obehr/phoniebox_hat/simulation/CutOff.asc

B1: bv; P=2.5
C1: cap; 100n
C2: cap; 100n
C3: cap; 100n
D1: schottky
D2: schottky
M1: pmos; AO3401A
M2: nmos; 2N7002
R1: res; 100k
R2: res; 1k
R3: res; 10k
R4: res; 100k
R5: res; 1k
R6: res; 10k
S1: sw; MySw
S2: sw; GPIO
U1: LT3008-3.3
V1: voltage; 5
V2: voltage; PULSE(0 1 50m 1n 1n 1s)
V3: voltage; PULSE(0 1 1m 1n 1n 10m)
Named nets: V_In, V_Out, G1, 0, 3P3, Ctrl_Out, Pressed, Keep, PowerOff, Ctrl_In, G2
.ic V(Keep)=0
.tran 100m
.model MySw SW(Vt=0.5 Ron=0.1)
Raspberry
Button
.model GPIO SW(Vt=0.5 Ron=200)
.include AO3401A.mod
GPIO17
3v3 Power
5v Power
GPIO4
Cut-Off Circuit
