obehr/phoniebox_hat/simulation/Debounce.asc

A1: schmitt; vt=1.3 vh=0.4
C1: cap; 1µ
R1: res; 33k
R2: res; 33k
S1: sw; MySw
V1: voltage; 3.3
V2: voltage; PULSE(0 1 {ton} 1n 1n {ton})
Named nets: 0, Pin, Button_Closed, Digital, 3P3
.model MySw SW(Vt=0.5)
.step dec param ton 1m 100m 1
.tran 400m
GPIO Schmitt Input
GPIO specifications see
https://www.raspberrypi.com/documentation/computers/raspberry-pi.html#voltage-specifications
